jerryok826/Lab-Power-Supply/Hardware/Altium/lps_regulator_rev_11/asof.082420/lps_regulator_rev_10.pdf

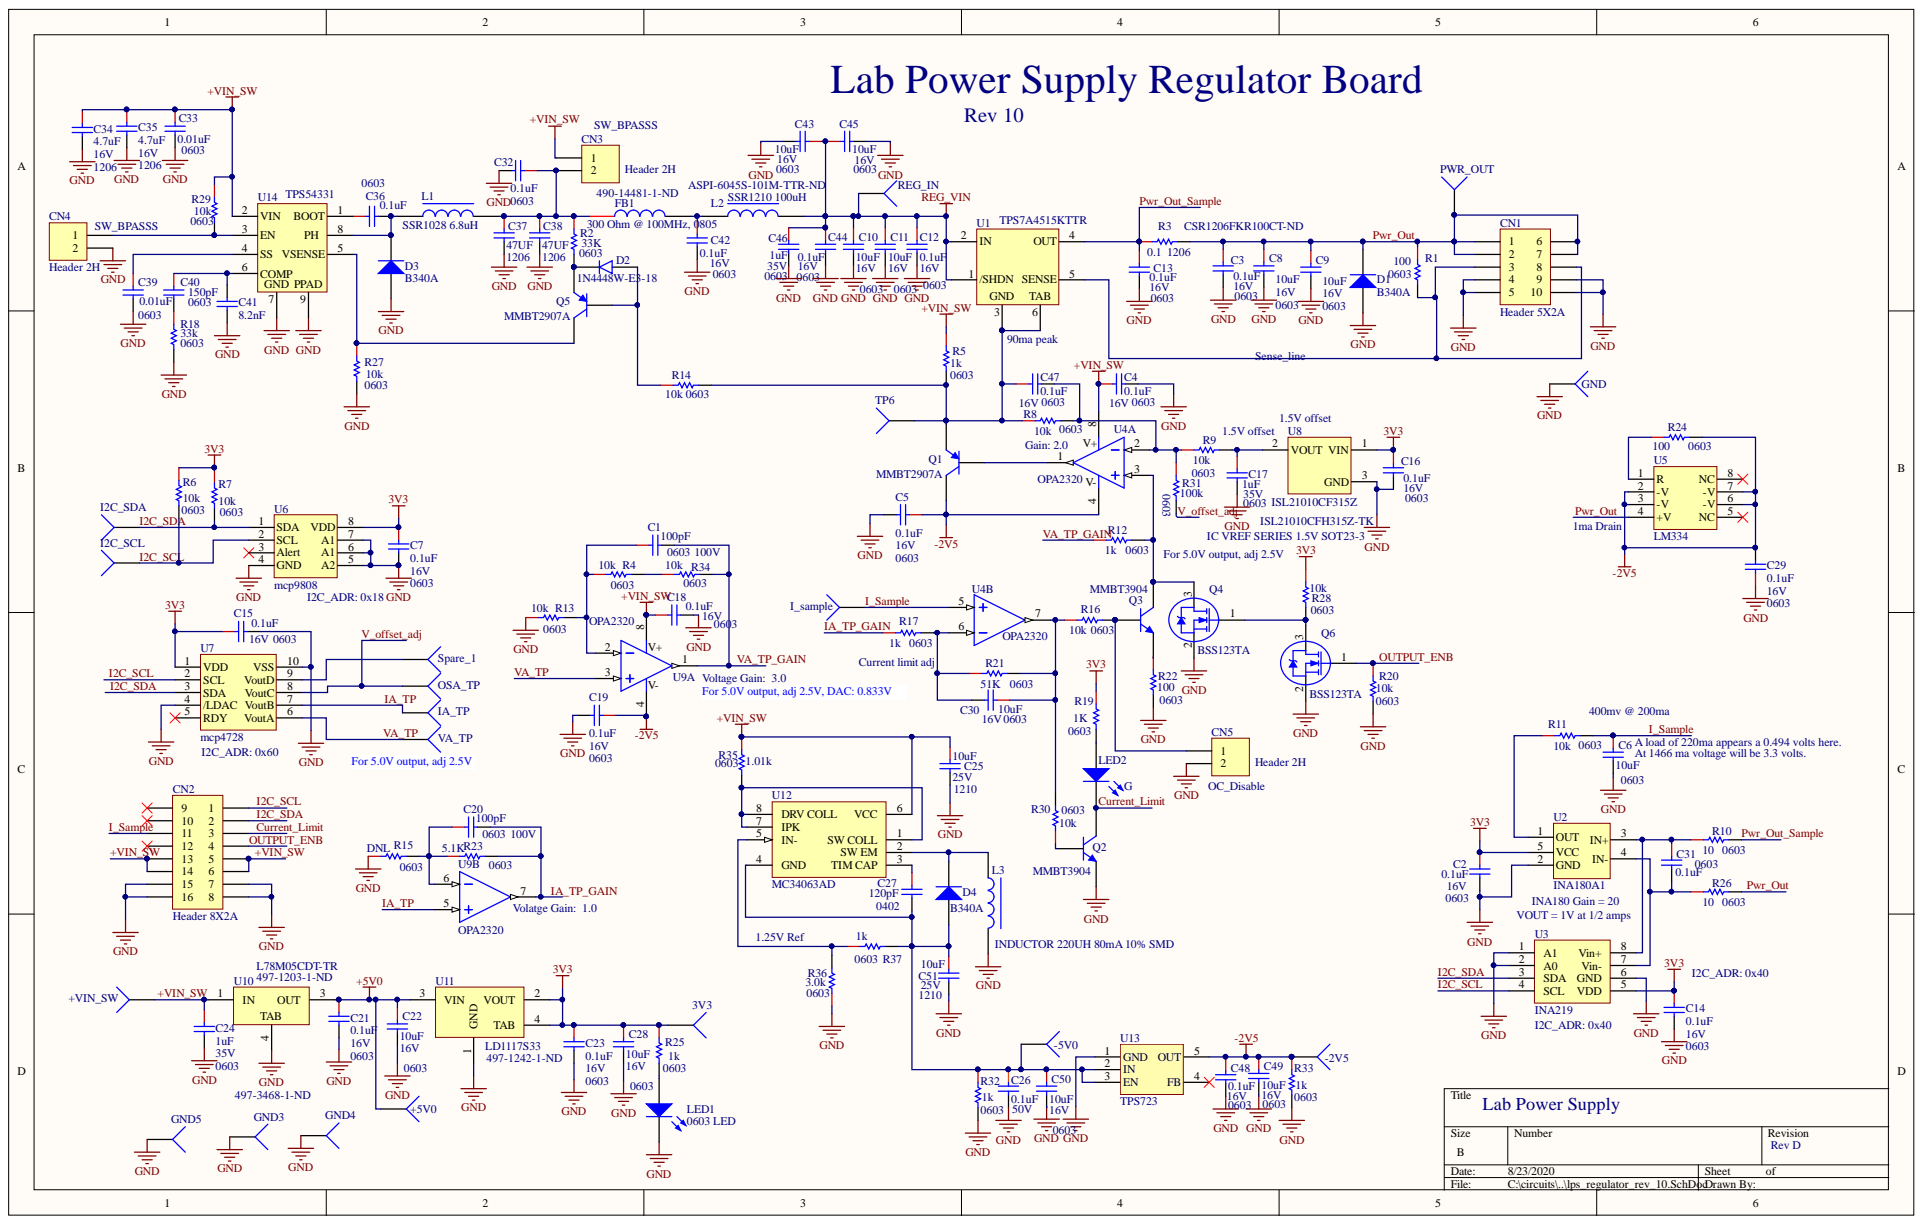
[picture p19: page 1]

Lab Power Supply Regulator Board

V+ | U4A | GND

RDY 5 VoutA SCL 2 SDA 3 | 6 VoutB 7 VoutC 8 VoutD 9 VSS 10

/LDAC 4 | | IA_TP

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


Comment | Description | Designator | Footprint | LibRef | Quantity
TestPoint_BLK | Test Point -Black | -2V5, -5V0, +5V0, +VTestPoin t-TH 42 mil | CMP-0 05-021 0-01 | 19
100pF | CAP CER100PF 50V 5C1,C20 | CAPC0603(1608)_N | CMP-007-0074-08 | 2
0.1uF | CAP CER0.1UF 16V 1C2, C,C13,C18, C19CAPC0 603(1608)_M | CMP-007-0042-08 | 9
0.1uF | CAP CER0.1UF 16V 1C3,C4, C5,C12, C14,CAPC0603(1608 )_N | CMP-007-0042-08 | 13
10uF | CAP CER10UF 16V X5C6,C8, C9, C10, C11,CAPC0603(1608 )_N | CMP-001-0603-12 | 11
1uF | CAP CER1UF 35V 10%C17,C24,C46 | CAPC0603(1608)_M | CMP-007-0109-08 | 3
10uF | CAP CER10UF 25V JB C25,C51 | CAPC1210(3225)_L | CMP-007-0085-08 | 2
0.1uF | 0.1uF 0805 50V | C26 | CAPC0805(2012)_N | CAP CER0.1UF 50V 1 | 1
120pF | CAP CER100PF 50V CC27 | CAPC0402(1005)_L | CMP-001-0595-08 | 1
10uF | CAP CER0.1UF 16V 1C30 | CAPC0603(1608)_M | CMP-007-0042-08 | 1
0.01uF | CAP CER0.01uF 50V C33, C39 | CAPC0603(1608)_N | CMP-007-0028-08, C | 2
4.7uF | CAP CER4.7UF 50V 1C34,C35 | CAPC1206(3216)_N | CMP-007-0147-08 | 2
47UF | CAP CER47UF 25V 12C37, C38 | CAPC1206(3216)_L | CMP-001-0623-11 | 2
150pF | CAP CER1UF 35V 10%C40 | CAPC0603(1608)_M | CMP-007-0109-08 | 1
8.2nF | CAP CER820PF 50V X7C41 | CAPC1608X87X35ML1CMP-001-0751-01 | 1
Header 5X2A | Header, 5-Pin, DualroCN1 | HDR2X5_CEN | CMP-001-0310-01 | 1
Header 8X2A | Header, 8-Pin, DualroCN2 | HDR2X8_CEN | CMP-001-0325-01 | 1
Header 2H | Header, 2-Pin, Right ACN3, CN4, CN5 | HDR1X2H | CMP-001-0287-01 | 3
B340A | DIODE SCHOTTKY 60D1,D3, D4 | DO-214AC | CMP-001-0130-02 | 3
1N4448W-E3-18 | Diodes -GeneralPurpD2 | SOD123 | CMP-001-0983-02 | 1
300 Ohm @ 100MHz, 600Ohms@ 100MHzFB1 | RESC0805(2012)_N | CM P-007-0197-02 | 1
SSR1028 6.8uH | INDUCTOR6.8uH SML1 | SRU1028 | CMP-001-0686-01 | 1
SSR1210 100uH | INDUCTOR100uH 2.L2 | SRR1210 | CMP-001-0686-01 | 1
INDUCTOR220UH 80220uH 3218 | L3 | IND-3218 Chip | CMP-007-0244-01 | 1
0603 LED | 0603 SMDLED | LED1 | SM-LED-0603 | CMP-001-0009-04 | 1
G | 0603 SMDLED | LED2 | SM-LED-0603 | 0603 LED | 1
MMBT2907A | PNP GeneralPurposeQ1, Q5 | SOT23 | CMP-012-0075-02 | 2
MMBT3904 | NPN GeneralPurposeQ2, Q3 | SOT23 | MMBT3904 | 2
BSS123TA | MOSFET N-CH 100V 1Q4,Q6 | SOT23-3L | CMP-012-0021-01 | 2
100 | RES 100 OHM1% 1/1R1, R23,R24 | RESC0603(1608)_N | CMP-007-0349-12 | 3
10K | RES 10K OHM1/10WR2, R5,R6,R7, R8, RRESC0603(1608)_M | CMP-007-0359-12 | 14
0.33 | RES 0.33 OHM1% 1/R3 | RESC1206(3216)_N | CMP-007-0323-14 | 1
10k | RES 10K OHM0.1% 1R4, R13,R34 | RESC0603(1608)_L | CMP-007-0357-12 | 3
1.0K | RES 1K OHM1% 1/10R12,R15, R16, R17, RRESC060 3(1608)_M | CMP-007-0404-12 | 11
33K | RES 33K OHM1/10WR18 | RESC0603(1608)_N | CMP-007-0480-12 | 1
100K | RES 100K OHM1% 1/R21 | RESC0603(1608)_M | CMP-007-0353-12 | 1
1.01k | RES 1.01K OHM1/10R35 | RESC0603(1608)_M | CMP-007-0329-12 | 1
38.3K | RES 38.3K OHM1/10R36, R37 | RESC0603(1608)_L | CMP-007-0486-12 | 2
TPS7A4515KTTR | TPS7A4515KTTR, linU1 | TPS7A4515KTTR | TPS7A4515KTTR | 1
INA180A1 | | U2 | SOT-23-5_MC | INA180A1 | 1
INA219 | Current MonitorIC | U3 | INA219 | INA219 | 1
OPA2320 | Dual Single Supply RaU4, U9 | SOIC-8_NoPad | CMP-006-0027-01 | 2
LM334 | LM334, Current sourcU5 | LM334 | LM334 | 1
mcp9808 | | U6 | 8MSOP | mcp9808 | 1
mcp4728 | MCP4728 | U7 | MCP4728 | mcp4728 | 1
ISL21010CF315Z | | U8 | SOT23 | ISL21010CF315Z | 1
