jerryok826/Lab-Power-Supply/Software/STM32CubeIDE/Core/Src/main.c

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
/* Includes ------------------------------------------------------------------*/
#include "main.h"

/* USER CODE BEGIN Includes */
#include <string.h>
#include <stdio.h>

#include "main_loop.h"

/* USER CODE END Includes */

ADC_HandleTypeDef hadc1;

I2C_HandleTypeDef hi2c1;

SPI_HandleTypeDef hspi1;

UART_HandleTypeDef huart2;

/* USER CODE BEGIN PV */
//static const uint8_t TMP102_ADDR = 0x18 <<1; // Use 8-bit address
//static const uint8_t REG_TEMP = 0x05;

/* USER CODE END PV */

void SystemClock_Config(void);
static void MX_GPIO_Init(void);
static void MX_I2C1_Init(void);
static void MX_USART2_UART_Init(void);
static void MX_SPI1_Init(void);
static void MX_ADC1_Init(void);
/* USER CODE BEGIN PFP */
#define PUTCHAR_PROTOTYPE int __io_putchar(int ch)

/* USER CODE END PFP */

/**
  * @brief  The application entry point.
  * @retval int
  */
int main(void)
{
  /* MCU Configuration--------------------------------------------------------*/

  /* Reset of all peripherals, Initializes the Flash interface and the Systick. */
  HAL_Init();

  /* Configure the system clock */
  SystemClock_Config();

  /* Initialize all configured peripherals */
  MX_GPIO_Init();
  MX_I2C1_Init();
  MX_USART2_UART_Init();
  MX_SPI1_Init();
  MX_ADC1_Init();
  /* Infinite loop */
  /* USER CODE BEGIN WHILE */

  lps_setup();

  while (1)
  {
	lps_loop();

    /* USER CODE END WHILE */

    /* USER CODE BEGIN 3 */
  }
  /* USER CODE END 3 */
}

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
/* USER CODE BEGIN 4 */
// https://community.st.com/t5/stm32-mcus-products/how-to-setup-printf-to-print-message-to-console/td-p/174337
/**
  * @brief  Retargets the C library printf function to the USART.
  * @param  None
  * @retval None
  */
PUTCHAR_PROTOTYPE
{
  /* Place your implementation of fputc here */
  /* e.g. write a character to the USART1 and Loop until the end of transmission */
  HAL_UART_Transmit(&huart2, (uint8_t *)&ch, 1, 0xFFFF);

  return ch;
}
/* USER CODE END 4 */
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
