jerryok826/Lab-Power-Supply/Software/STM32CubeIDE/lps_stm32f103RTC6_test1.ioc

Mcu.UserName=STM32F103RCTx
PA0-WKUP.Signal=ADCx_IN0
PA1.Signal=ADCx_IN1
PA2.Signal=USART2_TX
PA3.Signal=USART2_RX
PA4.Signal=GPIO_Output
PA5.Signal=SPI1_SCK
PA6.Signal=SPI1_MISO
PA7.Signal=SPI1_MOSI
PB0.Signal=GPIO_Input
PB1.Signal=GPIO_Output
PB10.Signal=GPIO_Output
PB11.Signal=GPIO_Output
PB12.Signal=GPIO_Output
PB13.Signal=GPIO_Input
PB14.Signal=GPIO_Output
PB15.Signal=GPIO_Output
PB6.Signal=I2C1_SCL
PB7.Signal=I2C1_SDA
PB8.Signal=GPIO_Input
PB9.Signal=GPIO_Output
PC11.Signal=GPIO_Output
PC12.Signal=GPIO_Output
